pjaako/ProxVox/KiCad/ProxVox-wiring/amplifier.kicad_sch

## KiCad design KiCad/ProxVox-wiring/amplifier.kicad_sch (2026-07-21)

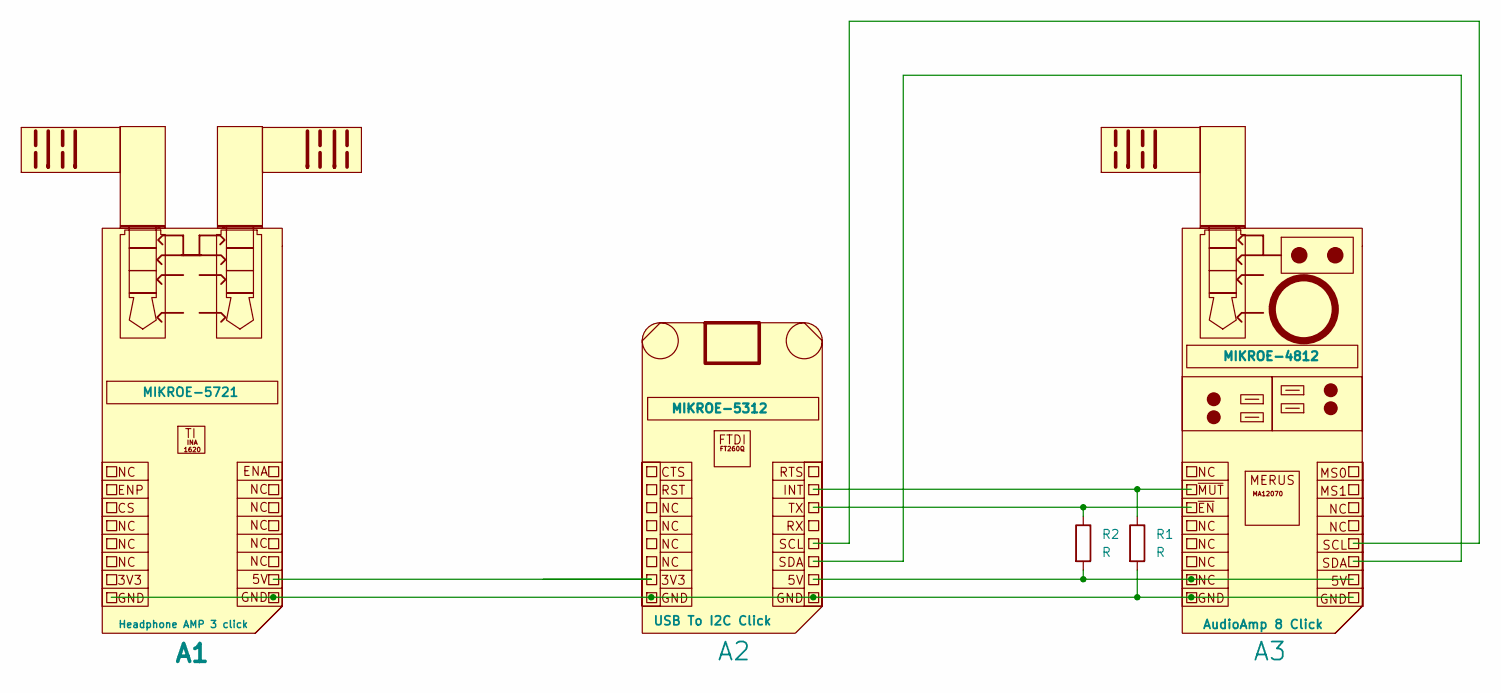
[picture p11: schematic amplifier.kicad_sch]

Parts:
A1: MIKROE-5721
A2: MIKROE-5312
A3: MIKROE-4812
R1, R2: R

Connections:
unnamed: A1.8 (GND), A1.9 (GND), A2.8 (GND), A2.9 (GND), A3.8 (GND), A3.9 (GND), R1.2
unnamed: A1.10 (3V3), A2.7 (+3.3V)
unnamed: A2.10 (+5V), A3., A3.10 (GND), R2.2
unnamed: A2.11 (SDA), A3.11 (SDA)
unnamed: A2.12 (SCL), A3.12 (SCL)
unnamed: A2.15 (INT), A3.2 (~MUTE), R1.1
unnamed: A2.16 (RTS), A3.3 (~ENABLE), R2.1
