pjaako/ProxVox/KiCad/ProxVox-wiring/power-button.kicad_sch

## KiCad design KiCad/ProxVox-wiring/power-button.kicad_sch (2026-07-21)

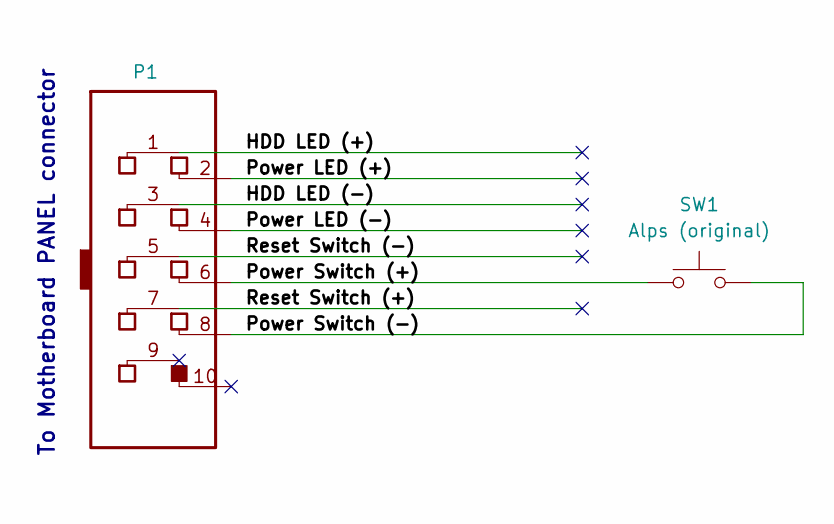
[picture p12: schematic power-button.kicad_sch]

Parts:
P1: (no value)
SW1: Alps (original)

Connections:
HDD LED (+): P1.1
HDD LED (-): P1.3
Power LED (+): P1.2
Power LED (-): P1.4
Power Switch (+): P1.6, SW1.1
Power Switch (-): P1.8, SW1.2
Reset Switch (+): P1.7
Reset Switch (-): P1.5

Notes on the sheet:
To Motherboard PANEL connector
